dhlav/TRS-IO/src/esp/components/trs-io/printer.cpp

#include "printer.h"

//----------------------------------------------------------------
static const char* m3toUnicode[] = {
  u8"\u0020", u8"\u00a3", u8"\u007c", u8"\u00e9", u8"\u00dc", u8"\u00c5", u8"\u00ac", u8"\u00f6", 
  u8"\u00d8", u8"\u00f9", u8"\u00f1", u8"\u0060", u8"\u0101", u8"\ue00d", u8"\u00c4", u8"\u00c3", 
  u8"\u00d1", u8"\u00d6", u8"\u00d8", u8"\u00d5", u8"\u00df", u8"\u00fc", u8"\u00f5", u8"\u00e6", 
  u8"\u00e4", u8"\u00e0", u8"\u0227", u8"\ue01b", u8"\u00c9", u8"\u00c6", u8"\u00c7", u8"\u02dc", 
  u8"\u0020", u8"\u0021", u8"\u0022", u8"\u0023", u8"\u0024", u8"\u0025", u8"\u0026", u8"\u0027", 
  u8"\u0028", u8"\u0029", u8"\u002a", u8"\u002b", u8"\u002c", u8"\u002d", u8"\u002e", u8"\u002f", 
  u8"\u0030", u8"\u0031", u8"\u0032", u8"\u0033", u8"\u0034", u8"\u0035", u8"\u0036", u8"\u0037", 
  u8"\u0038", u8"\u0039", u8"\u003a", u8"\u003b", u8"\u003c", u8"\u003d", u8"\u003e", u8"\u003f", 
  u8"\u0040", u8"\u0041", u8"\u0042", u8"\u0043", u8"\u0044", u8"\u0045", u8"\u0046", u8"\u0047", 
  u8"\u0048", u8"\u0049", u8"\u004a", u8"\u004b", u8"\u004c", u8"\u004d", u8"\u004e", u8"\u004f", 
  u8"\u0050", u8"\u0051", u8"\u0052", u8"\u0053", u8"\u0054", u8"\u0055", u8"\u0056", u8"\u0057", 
  u8"\u0058", u8"\u0059", u8"\u005a", u8"\u005b", u8"\u005c", u8"\u005d", u8"\u005e", u8"\u005f", 
  u8"\u0060", u8"\u0061", u8"\u0062", u8"\u0063", u8"\u0064", u8"\u0065", u8"\u0066", u8"\u0067", 
  u8"\u0068", u8"\u0069", u8"\u006a", u8"\u006b", u8"\u006c", u8"\u006d", u8"\u006e", u8"\u006f", 
  u8"\u0070", u8"\u0071", u8"\u0072", u8"\u0073", u8"\u0074", u8"\u0075", u8"\u0076", u8"\u0077", 
  u8"\u0078", u8"\u0079", u8"\u007a", u8"\u007b", u8"\u007c", u8"\u007d", u8"\u007e", u8"\u00b1", 
  u8"\ue080", u8"\ue081", u8"\ue082", u8"\ue083", u8"\ue084", u8"\ue085", u8"\ue086", u8"\ue087", 
  u8"\ue088", u8"\ue089", u8"\ue08a", u8"\ue08b", u8"\ue08c", u8"\ue08d", u8"\ue08e", u8"\ue08f", 
  u8"\ue090", u8"\ue091", u8"\ue092", u8"\ue093", u8"\ue094", u8"\ue095", u8"\ue096", u8"\ue097", 
  u8"\ue098", u8"\ue099", u8"\ue09a", u8"\ue09b", u8"\ue09c", u8"\ue09d", u8"\ue09e", u8"\ue09f", 
  u8"\ue0a0", u8"\ue0a1", u8"\ue0a2", u8"\ue0a3", u8"\ue0a4", u8"\ue0a5", u8"\ue0a6", u8"\ue0a7", 
  u8"\ue0a8", u8"\ue0a9", u8"\ue0aa", u8"\ue0ab", u8"\ue0ac", u8"\ue0ad", u8"\ue0ae", u8"\ue0af", 
  u8"\ue0b0", u8"\ue0b1", u8"\ue0b2", u8"\ue0b3", u8"\ue0b4", u8"\ue0b5", u8"\ue0b6", u8"\ue0b7", 
  u8"\ue0b8", u8"\ue0b9", u8"\ue0ba", u8"\ue0bb", u8"\ue0bc", u8"\ue0bd", u8"\ue0be", u8"\ue0bf", 
  u8"\u2660", u8"\u2665", u8"\u2666", u8"\u2663", u8"\u263a", u8"\u2639", u8"\u2264", u8"\u2265", 
  u8"\u03b1", u8"\u03b2", u8"\u03b3", u8"\u03b4", u8"\u03b5", u8"\u03b6", u8"\u03b7", u8"\u03b8", 
  u8"\u03b9", u8"\u03ba", u8"\u03bc", u8"\u03bd", u8"\u03be", u8"\u03bf", u8"\u03c0", u8"\u03c1", 
  u8"\u03c2", u8"\u03c3", u8"\u03c4", u8"\u03c5", u8"\u03c6", u8"\u03c7", u8"\u03c8", u8"\u03c9", 
  u8"\u2126", u8"\u221a", u8"\u00f7", u8"\u2211", u8"\u2248", u8"\u2206", u8"\u2307", u8"\u2260", 
  u8"\u2301", u8"\ue0e9", u8"\u237e", u8"\u221e", u8"\u2713", u8"\u00a7", u8"\u2318", u8"\u00a9", 
  u8"\u00a4", u8"\u00b6", u8"\u00a2", u8"\u00ae", u8"\ue0f4", u8"\ue0f5", u8"\ue0f6", u8"\u211e", 
  u8"\u2105", u8"\u2642", u8"\u2640", u8"\ue0fb", u8"\ue0fc", u8"\ue0fd", u8"\ue0fe", u8"\u2302"
};


const char* charToUTF8(const char ch)
{
  static const char* nl = "\n";

  return (ch == '\r') ? nl : m3toUnicode[(unsigned int) ch];
}
